joanperelopez/Modifications-TS-520/KICAD/mod_TS520.kicad_sch

## KiCad design KICAD/mod_TS520.kicad_sch (2023-10-10)

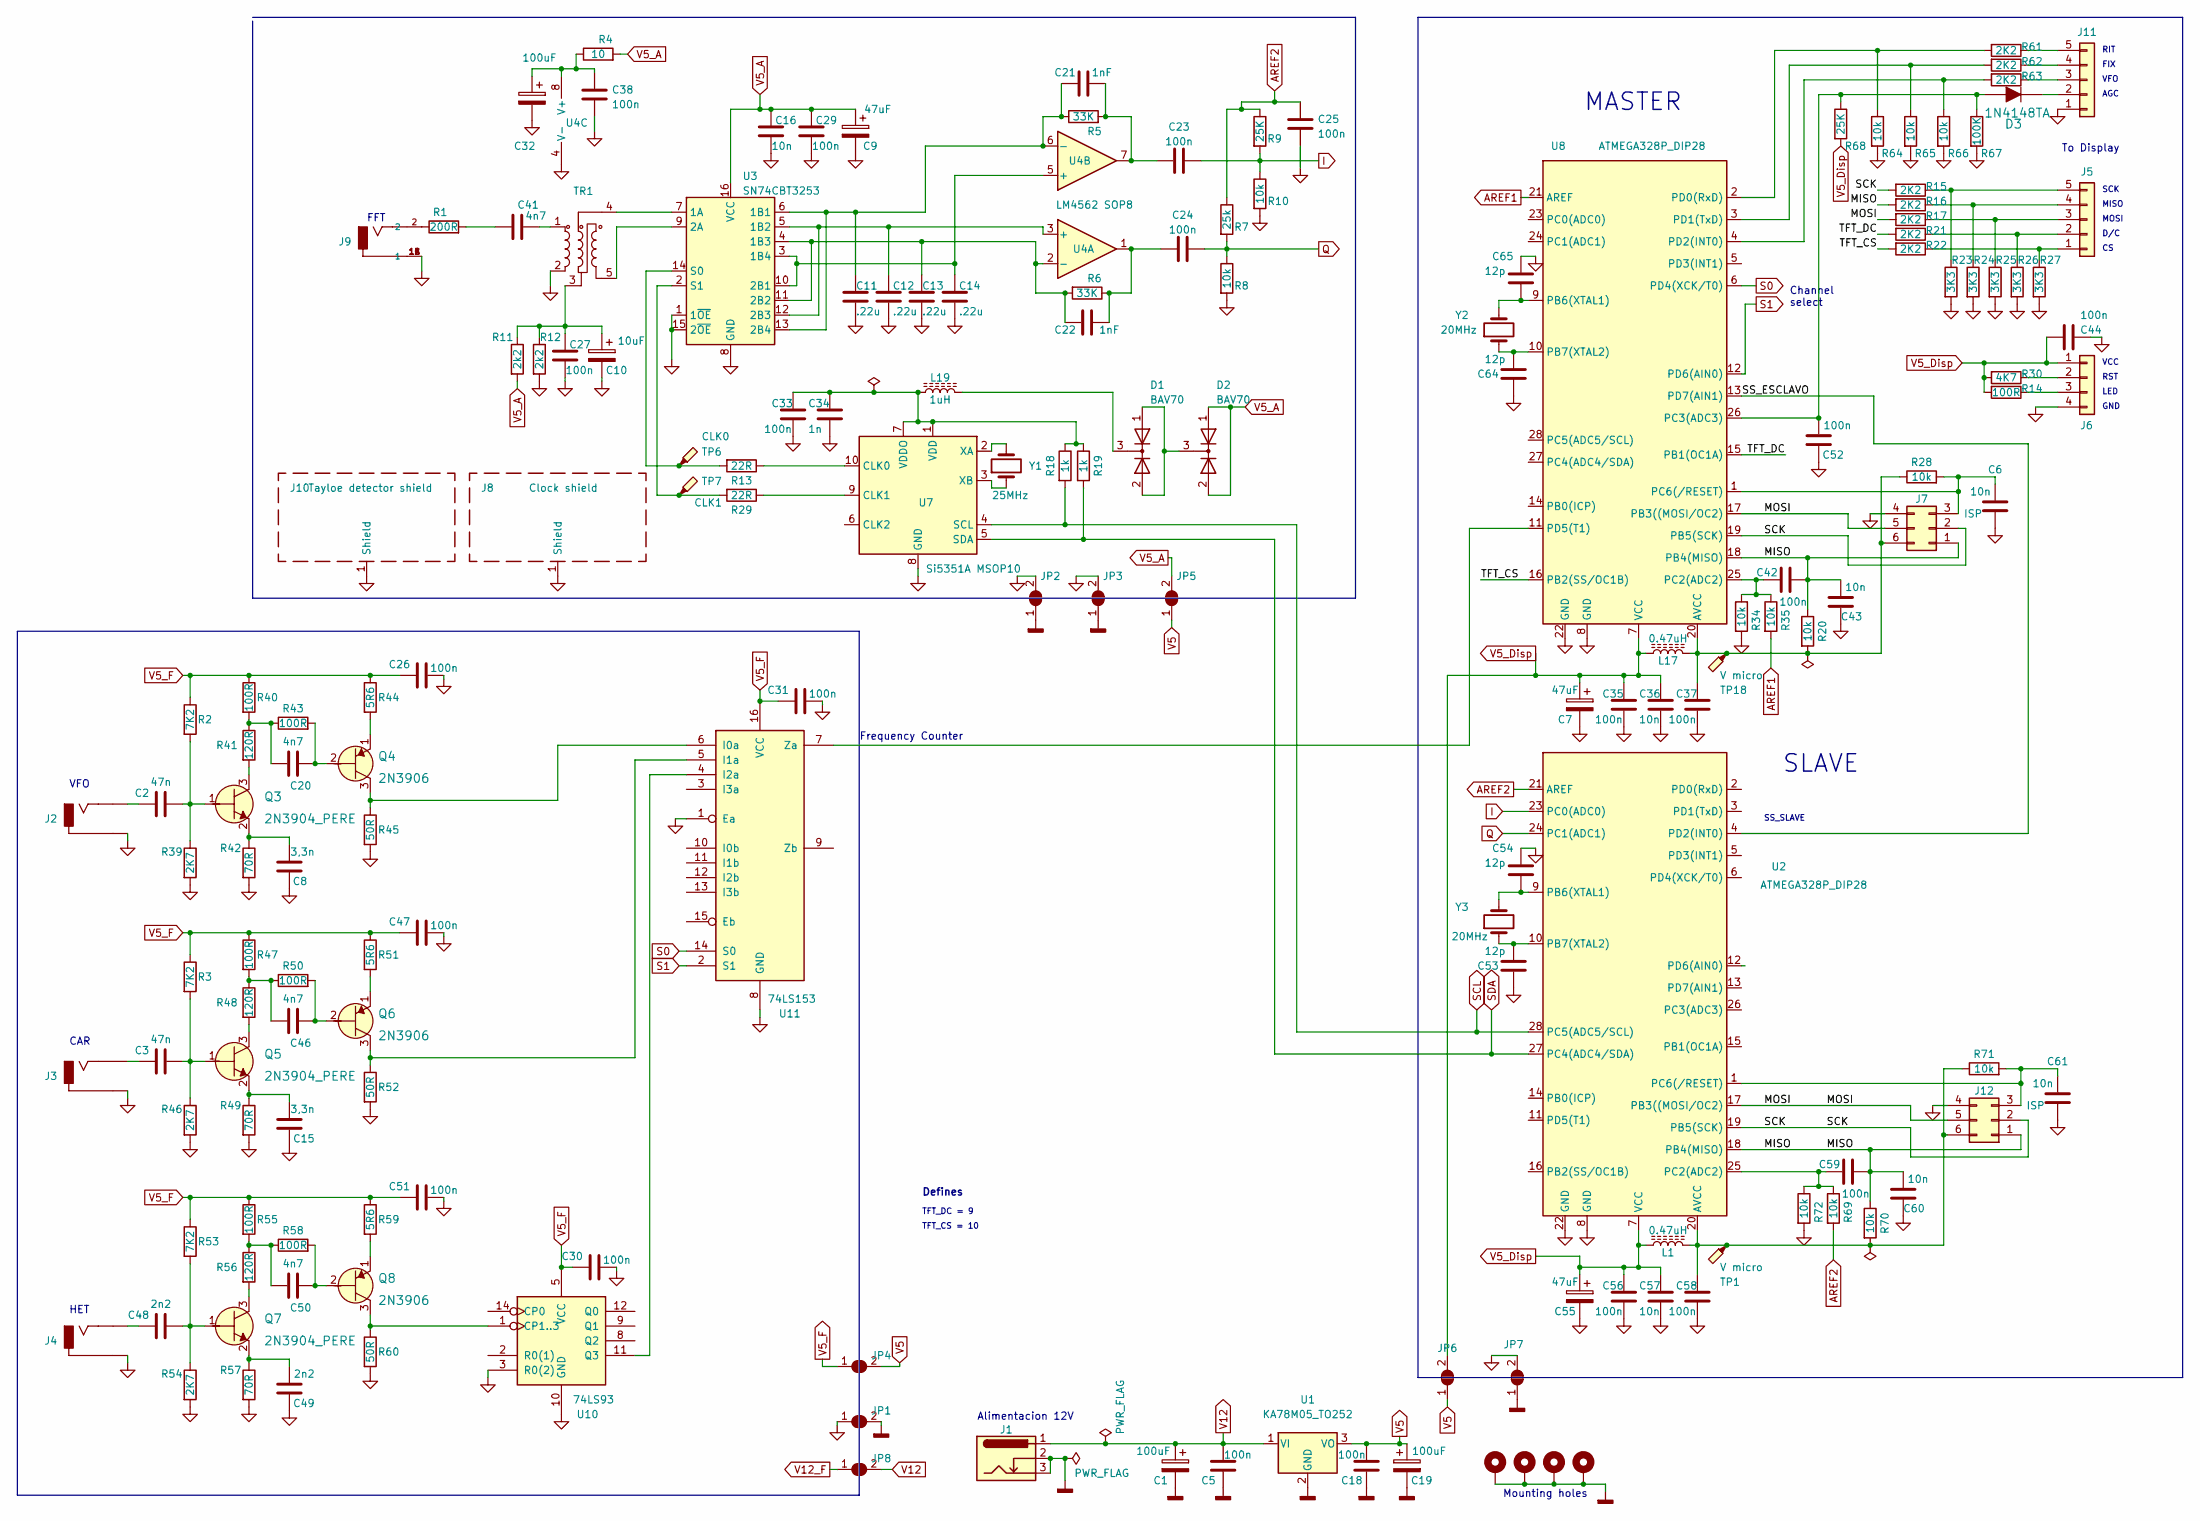
[picture p3: schematic mod_TS520.kicad_sch]

Parts:
C1: 100uF
C2, C3: 47n; C_0805_2012Metric
C5, C18, C23, C24, C25, C26, C27, C29, C30, C31, C33, C35, C37, C38, C42, C44, C47, C51, C52, C56, C58, C59: 100n; C_0805_2012Metric
C6, C16, C36, C43, C57, C60, C61: 10n; C_0805_2012Metric
C7, C9, C55: 47uF; L_Wuerth_MAPI-2512
C8, C15: 3,3n; C_0805_2012Metric
C10: 10uF; L_Wuerth_MAPI-2512
C11, C12, C13, C14: .22u; C_1206_3216Metric
C19, C32: 100uF; C_Elec_8x10.2
C20, C41, C46, C50: 4n7; C_0805_2012Metric
C21, C22: 1nF; C_0805_2012Metric
C34: 1n; C_0805_2012Metric
C48, C49: 2n2; C_0805_2012Metric
C53, C54, C64, C65: 12p; C_0805_2012Metric
D1, D2: BAV70; SOT-23
D3: 1N4148TA; DO-35; MPN 1N4148TA; Digi-Key_PN 1N4148TACT-ND
H9, H10, H11, H12: MountingHole_Pad; MountingHole_3.2mm_M3_Pad_TopBottom
J1: Barrel_Jack_Switch_Pin3Ring; BarrelJack_GCT_DCJ200-10-A_Horizontal
J2, J3, J4, J9: RCJ-013; CUI_RCJ-013; PART_REV B
J5, J11: Conn_01x05; JST_EH_B5B-EH-A_1x05_P2.50mm_Vertical
J6: Conn_01x04; JST_EH_B4B-EH-A_1x04_P2.50mm_Vertical
J7, J12: ISP; PinHeader_2x03_P2.54mm_Vertical
J8: Clock shield; Pere_Shielding_20x15mm
J10: Tayloe detector shield; Pere_RFShielding_20x25mm
JP1, JP2, JP3, JP4, JP5, JP6, JP7, JP8: SolderJumper_2_Open; SolderJumper-2_P1.3mm_Open_RoundedPad1.0x1.5mm
L1, L17: 0.47uH; L_1210_3225Metric_Pad1.42x2.65mm_HandSolder
L19: 1uH; L_1210_3225Metric_Pad1.42x2.65mm_HandSolder
Q3, Q5, Q7: 2N3904_PERE; SOT23-3; MPN 2N3904; Digi-Key_PN 2N3904CS-ND
Q4, Q6, Q8: 2N3906; SOT23-3; MPN 2N3906; Digi-Key_PN 2N3906CS-ND
R1: 200R; R_0805_2012Metric_Pad1.20x1.40mm_HandSolder
R2, R3, R53: 7K2; R_0805_2012Metric_Pad1.20x1.40mm_HandSolder
R4: 10; R_0805_2012Metric_Pad1.20x1.40mm_HandSolder
R5, R6: 33K; R_0805_2012Metric_Pad1.20x1.40mm_HandSolder
R7: 25k; R_0805_2012Metric_Pad1.20x1.40mm_HandSolder
R8, R10, R20, R28, R34, R35, R64, R65, R66, R69, R70, R71, R72: 10k; R_0805_2012Metric_Pad1.20x1.40mm_HandSolder
R9, R68: 25K; R_0805_2012Metric_Pad1.20x1.40mm_HandSolder
R11, R12: 2k2; R_0805_2012Metric_Pad1.20x1.40mm_HandSolder
R13, R29: 22R; R_0805_2012Metric_Pad1.20x1.40mm_HandSolder
R14, R40, R43, R47, R50, R55, R58: 100R; R_0805_2012Metric_Pad1.20x1.40mm_HandSolder
R15, R16, R17, R21, R22, R61, R62, R63: 2K2; R_0805_2012Metric_Pad1.20x1.40mm_HandSolder
R18, R19: 1k; R_0805_2012Metric_Pad1.20x1.40mm_HandSolder
R23, R24, R25, R26, R27: 3K3; R_0805_2012Metric_Pad1.20x1.40mm_HandSolder
R30: 4K7; R_0805_2012Metric_Pad1.20x1.40mm_HandSolder
R39, R46, R54: 2K7; R_0805_2012Metric_Pad1.20x1.40mm_HandSolder
R41, R48, R56: 120R; R_0805_2012Metric_Pad1.20x1.40mm_HandSolder
R42, R49, R57: 70R; R_0805_2012Metric_Pad1.20x1.40mm_HandSolder
R44, R51, R59: 5R6; R_0805_2012Metric_Pad1.20x1.40mm_HandSolder
R45, R52, R60: 50R; R_0805_2012Metric_Pad1.20x1.40mm_HandSolder
R67: 100K; R_0805_2012Metric_Pad1.20x1.40mm_HandSolder
TP1, TP18: V micro; TestPoint_Pad_D1.5mm
TP6: CLK0; TestPoint_Pad_D1.5mm
TP7: CLK1; TestPoint_Pad_D1.5mm
TR1: Toroid_trifilar_pere; Toroid_TR4to1_11mm
U1: KA78M05_TO252; TO-252
U2, U8: ATMEGA328P_DIP28; DIP28
U3: SN74CBT3253; TSSOP-16_4.4x5mm_P0.65mm
U4: LM4562 SOP8; SOP-8_3.76x4.96mm_P1.27mm
U7: Si5351A MSOP10; MSOP-10_3x3mm_P0.5mm
U10: 74LS93; DIP14
U11: 74LS153; SOP-16_4.55x10.3mm_P1.27mm
Y1: 25MHz; Crystal_SMD_HC49-SD
Y2, Y3: 20MHz; Crystal_SMD_HC49-SD

Connections:
AREF1: R35.2, U8.21 (AREF)
AREF2: C25.2, R7.1, R9.1, R69.2, U2.21 (AREF)
GND: C6.1, C7.2, C35.1, C36.1, C37.1, C43.2, C44.2, C52.2, C53.1, C54.2, C55.2, C56.1, C57.1, C58.1, C60.2, C61.1, C64.1, C65.2, J6.4, J7.4, J11.1, J12.4, JP7.2 (B), R23.2, R24.2, R25.2, R26.2, R27.2, R34.2, R64.2, R65.2, R66.2, R67.2, R72.2, U2.8 (GND), U2.22 (GND), U8.8 (GND), U8.22 (GND)
GND1: C8.2, C15.2, C26.1, C30.1, C31.1, C47.1, C49.2, C51.1, J2.1A (1), J2.1B (1), J2.1C (1), J3.1A (1), J3.1B (1), J3.1C (1), J4.1A (1), J4.1B (1), J4.1C (1), JP1.1 (A), R39.2, R42.2, R45.2, R46.2, R49.2, R52.2, R54.2, R57.2, R60.2, U10.3 (R0(2)), U10.10 (GND), U11.1 (Ea), U11.8 (GND)
GND2: C9.2, C10.2, C11.1, C12.1, C13.1, C14.1, C16.1, C25.1, C27.1, C29.1, C32.2, C38.1, J9.1A (1), J9.1B (1), J9.1C (1), J10.1, JP3.2 (B), R8.2, R10.2, R12.2, TR1.2, U3.1 (1~OE), U3.8 (GND), U3.15 (2~OE), U4.4 (V-)
GND3: C33.1, C34.1, J8.1, JP2.2 (B), U7.8 (GND)
GNDD: C1.2, C5.1, C18.1, C19.2, H9.1, H10.1, H11.1, H12.1, J1.2, J1.3, JP1.2 (B), JP2.1 (A), JP3.1 (A), JP7.1 (A), U1.2 (GND)
I: C23.2, R9.2, R10.1, U2.23 (PC0(ADC0))
MISO: C42.1, C43.1, C59.1, C60.1, J7.1, J12.1, R16.2, R20.1, R70.1, U2.18 (PB4(MISO)), U8.18 (PB4(MISO))
MOSI: J7.5, J12.5, R17.2, U2.17 (PB3((MOSI/OC2)), U8.17 (PB3((MOSI/OC2))
unnamed: C2.1, Q3.1 (B), R2.2, R39.1
unnamed: C2.2, J2.2
unnamed: C3.1, Q5.1 (B), R3.2, R46.1
unnamed: C3.2, J3.2
unnamed: C6.2, J7.3, R28.2, U8.1 (PC6(/RESET))
unnamed: C8.1, Q3.2 (E), R42.1
unnamed: C10.1, C27.2, R11.1, R12.1, TR1.3
unnamed: C11.2, C21.1, R5.1, U3.6 (1B1), U3.13 (2B4), U4.6 (-)
unnamed: C12.2, U3.5 (1B2), U3.12 (2B3), U4.3 (+)
unnamed: C13.2, C22.2, R6.2, U3.4 (1B3), U3.11 (2B2), U4.2 (-)
unnamed: C14.2, U3.3 (1B4), U3.10 (2B1), U4.5 (+)
unnamed: C15.1, Q5.2 (E), R49.1
unnamed: C20.1, R40.2, R41.1, R43.1
unnamed: C20.2, Q4.2 (B), R43.2
unnamed: C21.2, C23.1, R5.2, U4.7
unnamed: C22.1, C24.1, R6.1, U4.1
unnamed: C32.1, C38.2, R4.1, U4.8 (V+)
unnamed: C33.2, C34.2, L19.1, R18.1, R19.1, U7.1 (VDD), U7.7 (VDDO)
unnamed: C37.2, J7.6, L17.2, R20.2, R28.1, TP18.1, U8.20 (AVCC)
unnamed: C41.1, TR1.1
unnamed: C41.2, R1.2
unnamed: C42.2, R34.1, R35.1, U8.25 (PC2(ADC2))
unnamed: C46.1, R47.2, R48.1, R50.1
unnamed: C46.2, Q6.2 (B), R50.2
unnamed: C48.1, Q7.1 (B), R53.2, R54.1
unnamed: C48.2, J4.2
unnamed: C49.1, Q7.2 (E), R57.1
unnamed: C50.1, R55.2, R56.1, R58.1
unnamed: C50.2, Q8.2 (B), R58.2
unnamed: C52.1, D3.A, R67.1, R68.1, U8.26 (PC3(ADC3))
unnamed: C53.2, U2.10 (PB7(XTAL2)), Y3.1
unnamed: C54.1, U2.9 (PB6(XTAL1)), Y3.2
unnamed: C58.2, J12.6, L1.2, R70.2, R71.1, TP1.1, U2.20 (AVCC)
unnamed: C59.2, R69.1, R72.1, U2.25 (PC2(ADC2))
unnamed: C61.2, J12.3, R71.2, U2.1 (PC6(/RESET))
unnamed: C64.2, U8.10 (PB7(XTAL2)), Y2.1
unnamed: C65.1, U8.9 (PB6(XTAL1)), Y2.2
unnamed: D1.1 (A), D1.2 (A), D2.3 (K)
unnamed: D1.3 (K), L19.2
unnamed: D3.K, J11.2
unnamed: J5.1, R22.1, R27.1
unnamed: J5.2, R21.1, R26.1
unnamed: J5.3, R17.1, R25.1
unnamed: J5.4, R16.1, R24.1
unnamed: J5.5, R15.1, R23.1
unnamed: J6.2, R30.1
unnamed: J6.3, R14.1
unnamed: J9.2, R1.1
unnamed: J11.3, R63.1
unnamed: J11.4, R62.1
unnamed: J11.5, R61.1
unnamed: Q3.3 (C), R41.2
unnamed: Q4.1 (E), R44.2
unnamed: Q4.3 (C), R45.1, U11.6 (I0a)
unnamed: Q5.3 (C), R48.2
unnamed: Q6.1 (E), R51.2
unnamed: Q6.3 (C), R52.1, U11.5 (I1a)
unnamed: Q7.3 (C), R56.2
unnamed: Q8.1 (E), R59.2
unnamed: Q8.3 (C), R60.1, U10.1 (CP1..3)
unnamed: R13.1, U7.10 (CLK0)
unnamed: R13.2, TP6.1, U3.14 (S0)
unnamed: R29.1, U7.9 (CLK1)
unnamed: R29.2, TP7.1, U3.2 (S1)
unnamed: R61.2, R64.1, U8.2 (PD0(RxD))
unnamed: R62.2, R65.1, U8.3 (PD1(TxD))
unnamed: R63.2, R66.1, U8.4 (PD2(INT0))
unnamed: TR1.4, U3.7 (1A)
unnamed: TR1.5, U3.9 (2A)
unnamed: U7.2 (XA), Y1.2
unnamed: U7.3 (XB), Y1.1
unnamed: U10.11 (Q3), U11.4 (I2a)
unnamed: U8.11 (PD5(T1)), U11.7 (Za)
Q: C24.2, R7.2, R8.1, U2.24 (PC1(ADC1))
S0: U8.6 (PD4(XCK/T0)), U11.14 (S0)
S1: U8.12 (PD6(AIN0)), U11.2 (S1)
SCK: J7.2, J12.2, R15.2, U2.19 (PB5(SCK)), U8.19 (PB5(SCK))
SCL: R18.2, U2.28 (PC5(ADC5/SCL)), U7.4 (SCL)
SDA: R19.2, U2.27 (PC4(ADC4/SDA)), U7.5 (SDA)
SS_ESCLAVO: U2.4 (PD2(INT0)), U8.13 (PD7(AIN1))
TFT_CS: R22.2, U8.16 (PB2(SS/OC1B))
TFT_DC: R21.2, U8.15 (PB1(OC1A))
V5: C18.2, C19.1, JP4.2 (B), JP5.1 (A), JP6.1 (A), U1.3 (VO)
V5_A: C9.1, C16.2, C29.2, D2.1 (A), D2.2 (A), JP5.2 (B), R4.2, R11.2, U3.16 (VCC)
V5_Disp: C7.1, C35.2, C36.2, C44.1, C55.1, C56.2, C57.2, J6.1, JP6.2 (B), L1.1, L17.1, R14.2, R30.2, R68.2, U2.7 (VCC), U8.7 (VCC)
V5_F: C26.2, C30.2, C31.2, C47.2, C51.2, JP4.1 (A), R2.1, R3.1, R40.1, R44.1, R47.1, R51.1, R53.1, R55.1, R59.1, U10.5 (VCC), U11.16 (VCC)
V12: C1.1, C5.2, J1.1, JP8.2 (B), U1.1 (VI)
V12_F: JP8.1 (A)

Notes on the sheet:
D/C
SCK
MOSI
Channel select
CAR
To Display
Frequency Counter
VFO
RIT
FIX
Defines
VCC
TFT_CS = 10
LED
FFT
MASTER
TFT_DC = 9
GND
SLAVE
HET
Alimentacion 12V
AGC
SS_SLAVE
MISO
Mounting holes
RST
